alorman/esp32-backpack/ESP Backpack/Outputs/Images/esp32-backpack-front.png

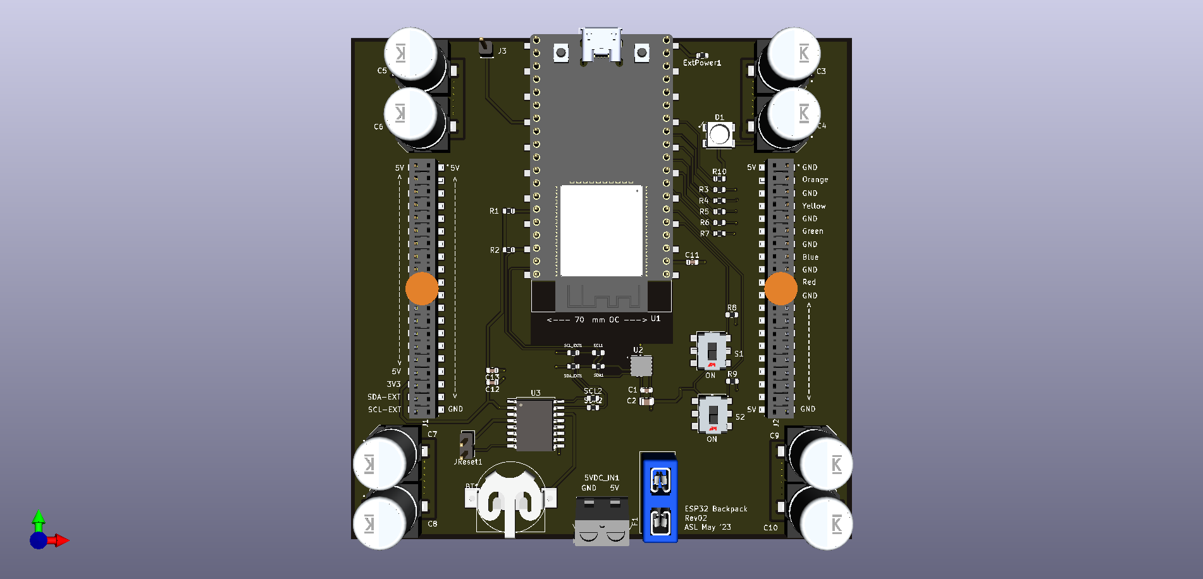
ESP Backpack/Outputs/Images/esp32-backpack-front.png
